ArthurAdmiraal/Squidpad/Documentation/Sysdiagram.png

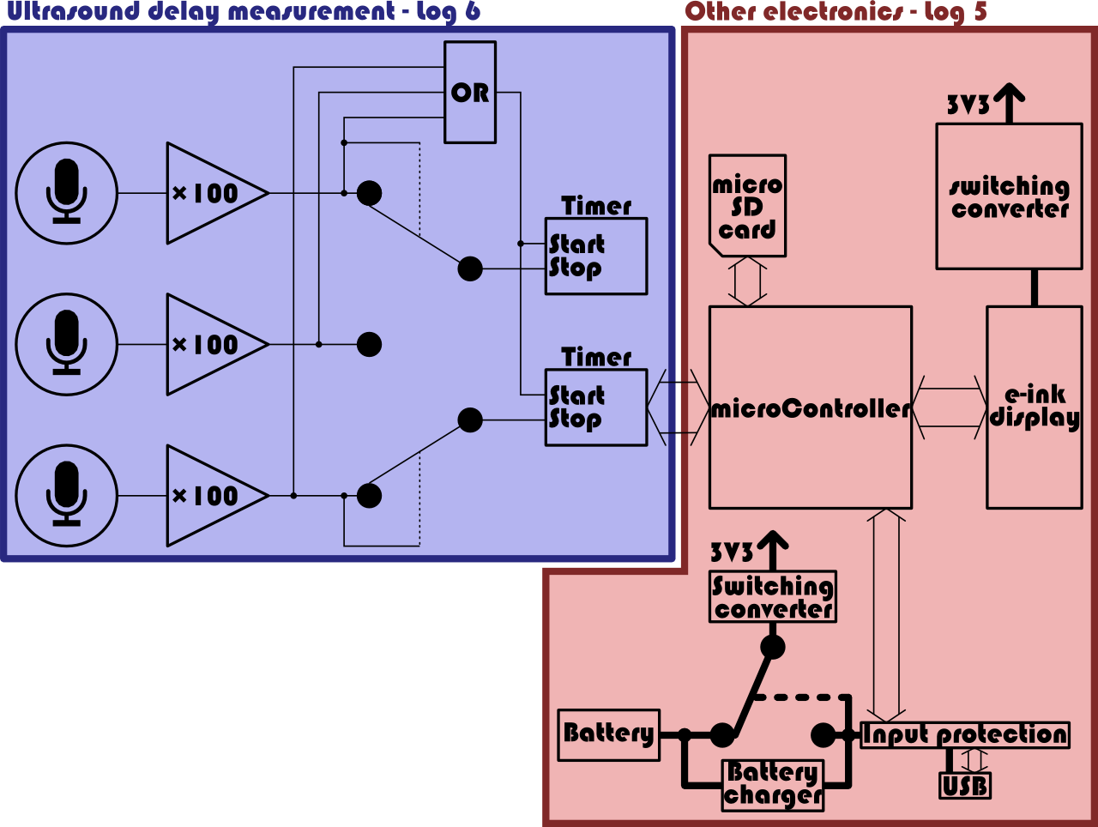
Documentation/Sysdiagram.png
