ArthurAdmiraal/Squidpad/Documentation/TrilaterationDiagram.png

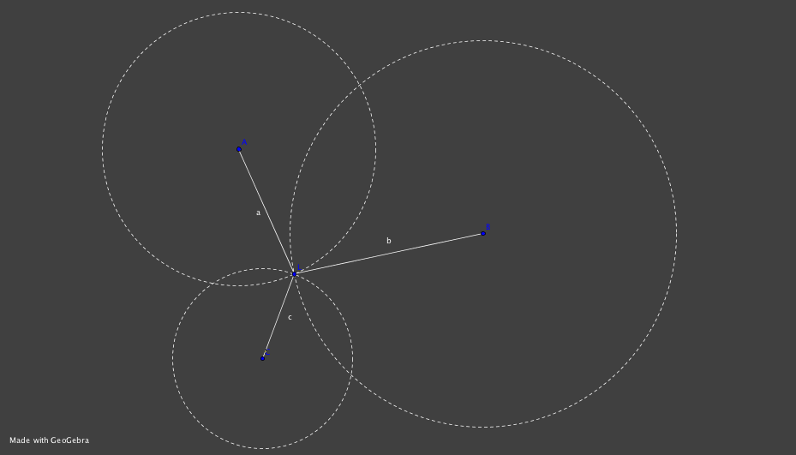
Documentation/TrilaterationDiagram.png
